pavelzazvorka-ctrl/AltiVario/doc/img/20200905_162352.jpg

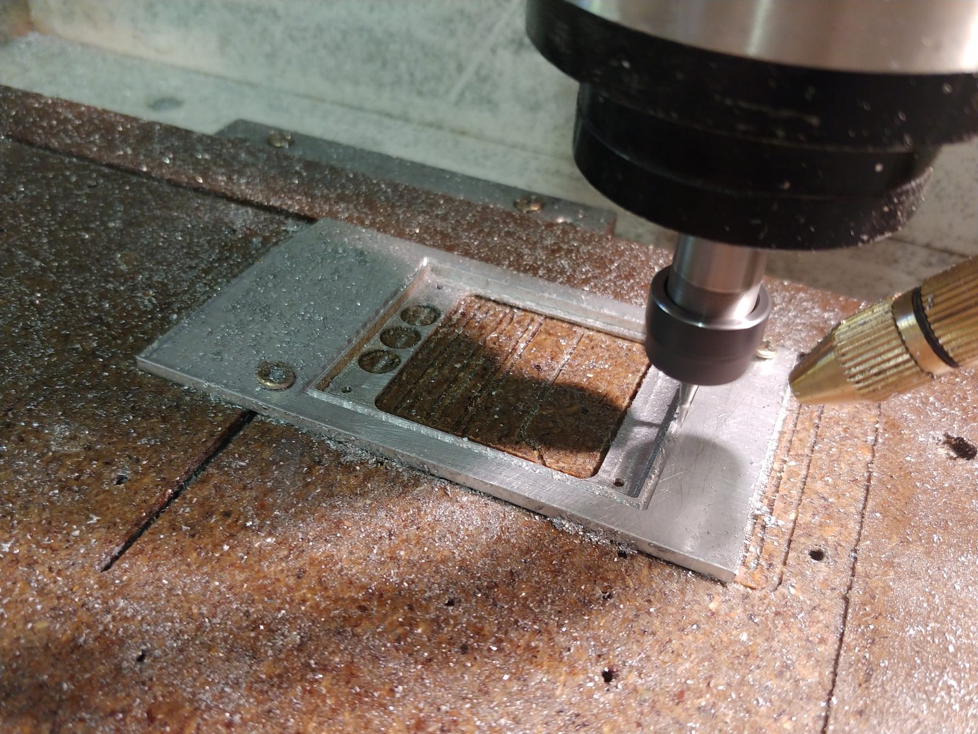
doc/img/20200905_162352.jpg
