pavelzazvorka-ctrl/AltiVario/doc/img/20200905_163800_HDR.jpg

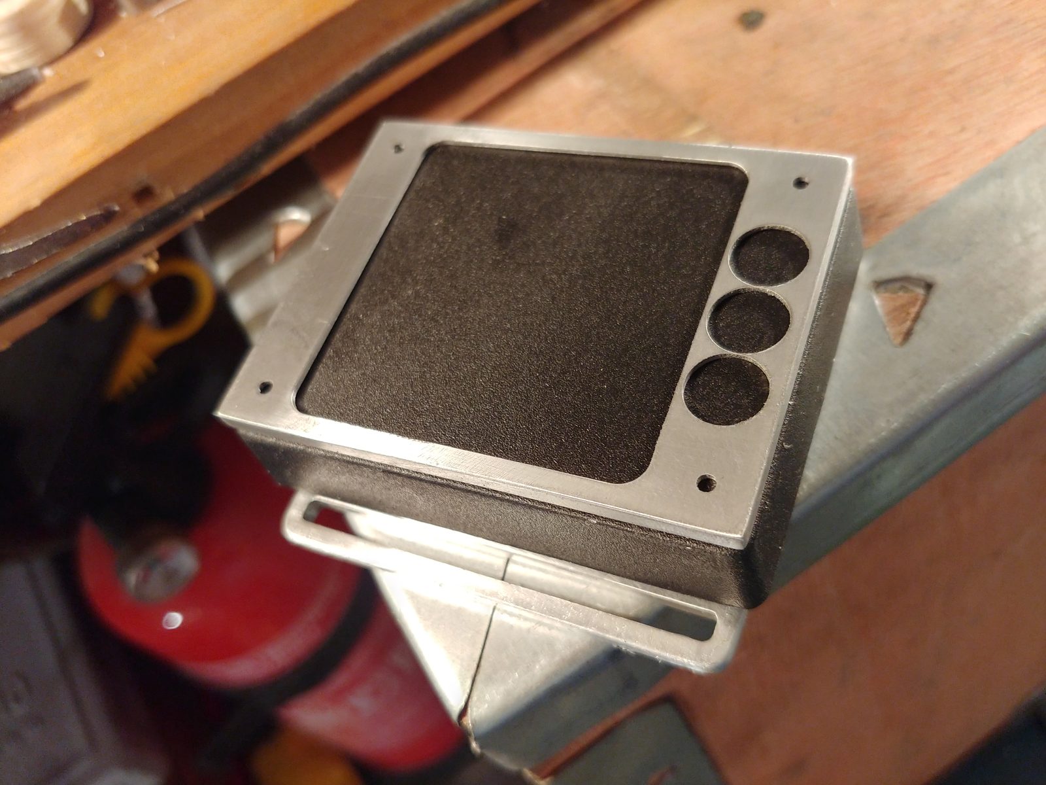
doc/img/20200905_163800_HDR.jpg
