pavelzazvorka-ctrl/AltiVario/doc/img/20200905_175942_HDR.jpg

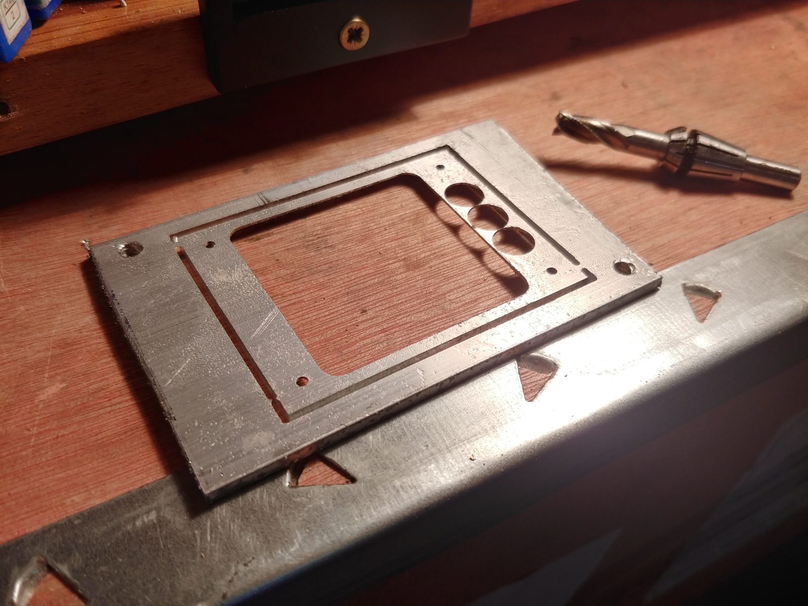
doc/img/20200905_175942_HDR.jpg
