pavelzazvorka-ctrl/AltiVario/doc/img/20200926_111940.jpg

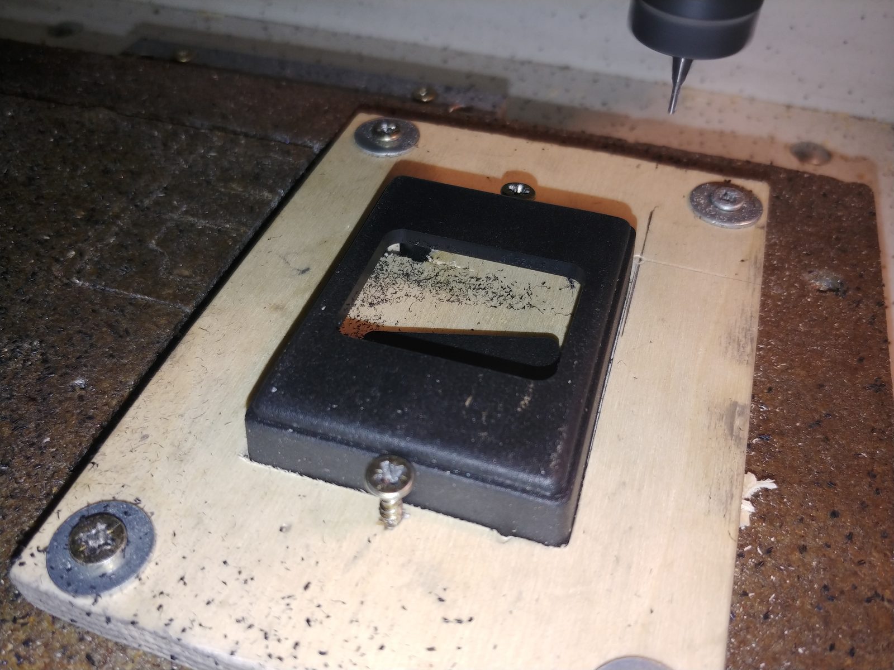
doc/img/20200926_111940.jpg
