pavelzazvorka-ctrl/AltiVario/doc/img/20200926_113900_HDR.jpg

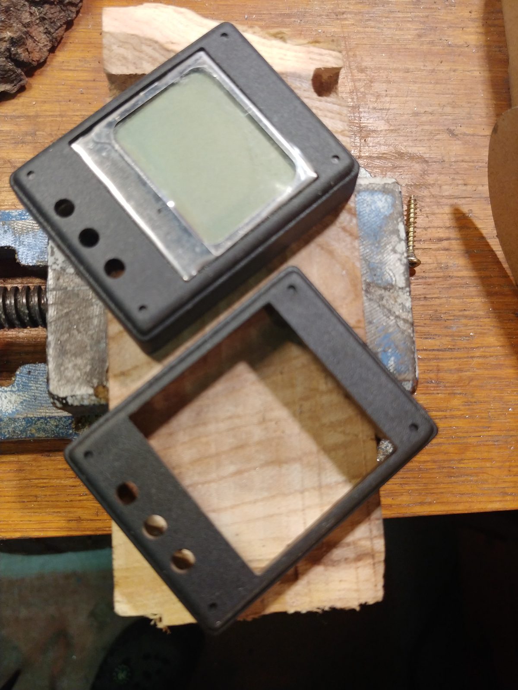
doc/img/20200926_113900_HDR.jpg
