pavelzazvorka-ctrl/AltiVario/doc/img/20200926_113952.jpg

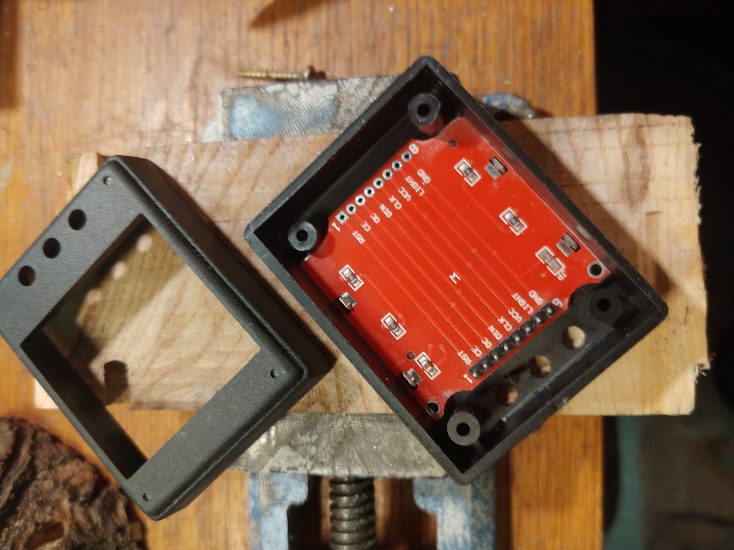
doc/img/20200926_113952.jpg
