pavelzazvorka-ctrl/AltiVario/doc/img/20200926_114129_HDR.jpg

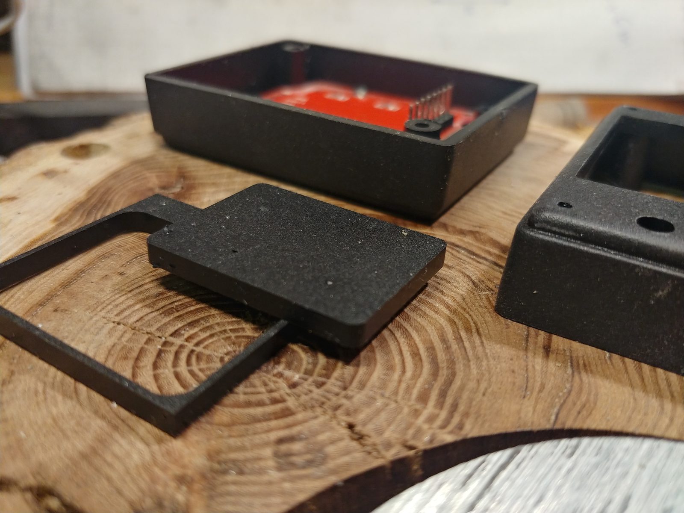
doc/img/20200926_114129_HDR.jpg
