pavelzazvorka-ctrl/AltiVario/doc/img/20200926_120201.jpg

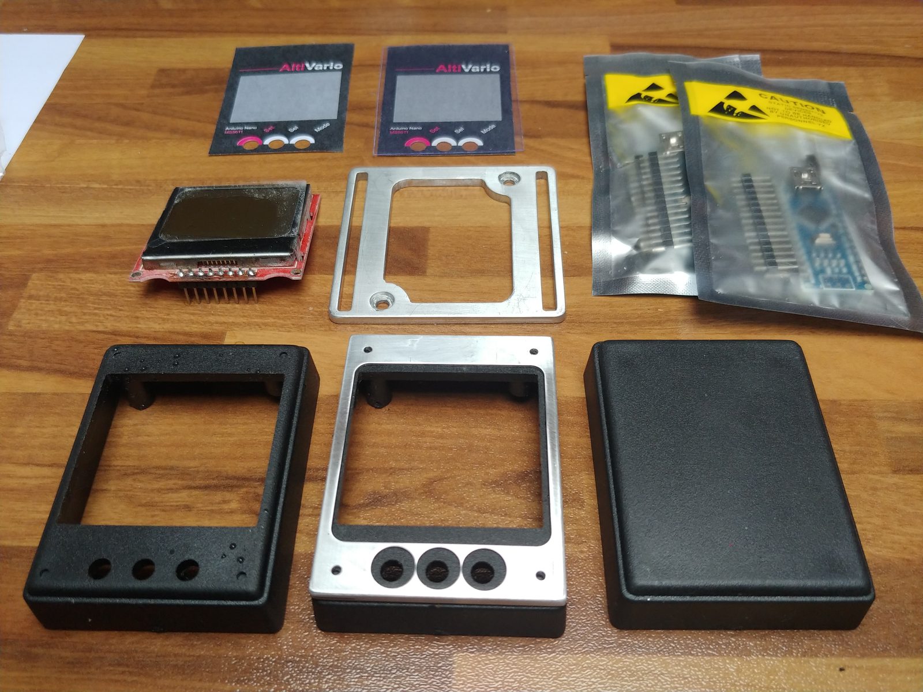
doc/img/20200926_120201.jpg
