pavelzazvorka-ctrl/AltiVario/doc/img/20200926_120225.jpg

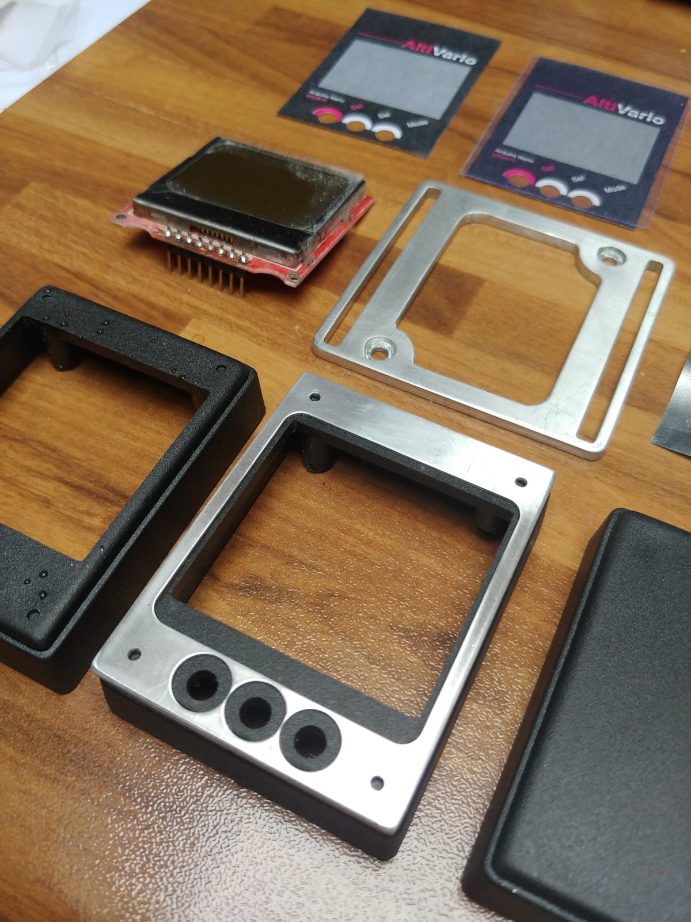
doc/img/20200926_120225.jpg
