pavelzazvorka-ctrl/AltiVario/doc/img/20200926_160403.jpg

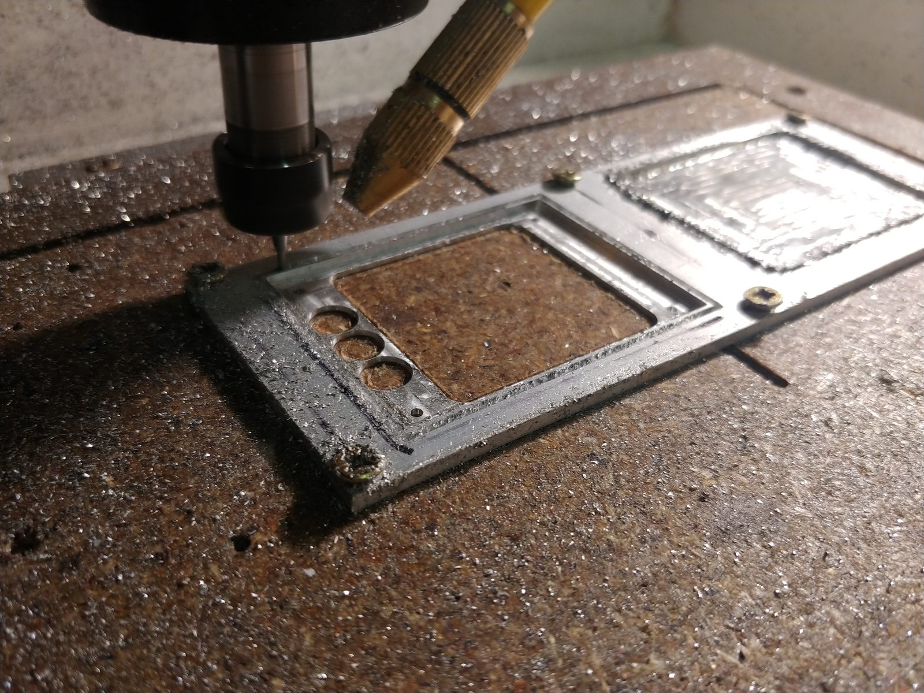
doc/img/20200926_160403.jpg
