pavelzazvorka-ctrl/AltiVario/doc/img/20200926_190031.jpg

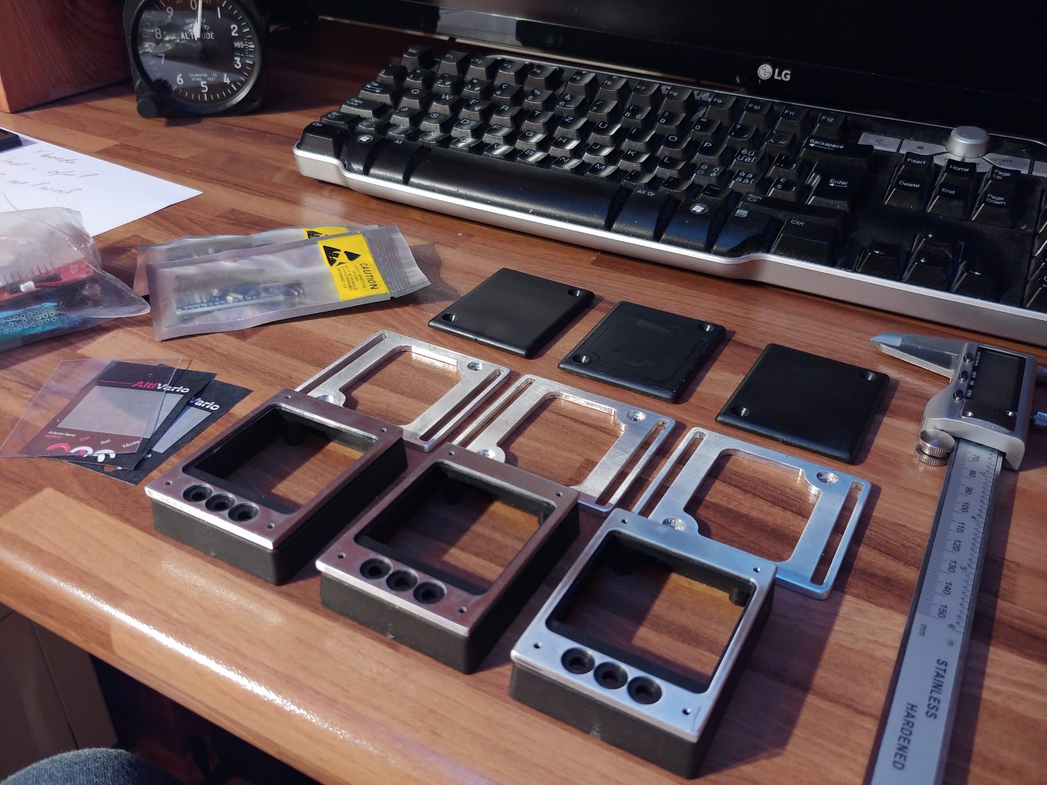
doc/img/20200926_190031.jpg
