pavelzazvorka-ctrl/AltiVario/doc/img/20200926_190852_HDR.jpg

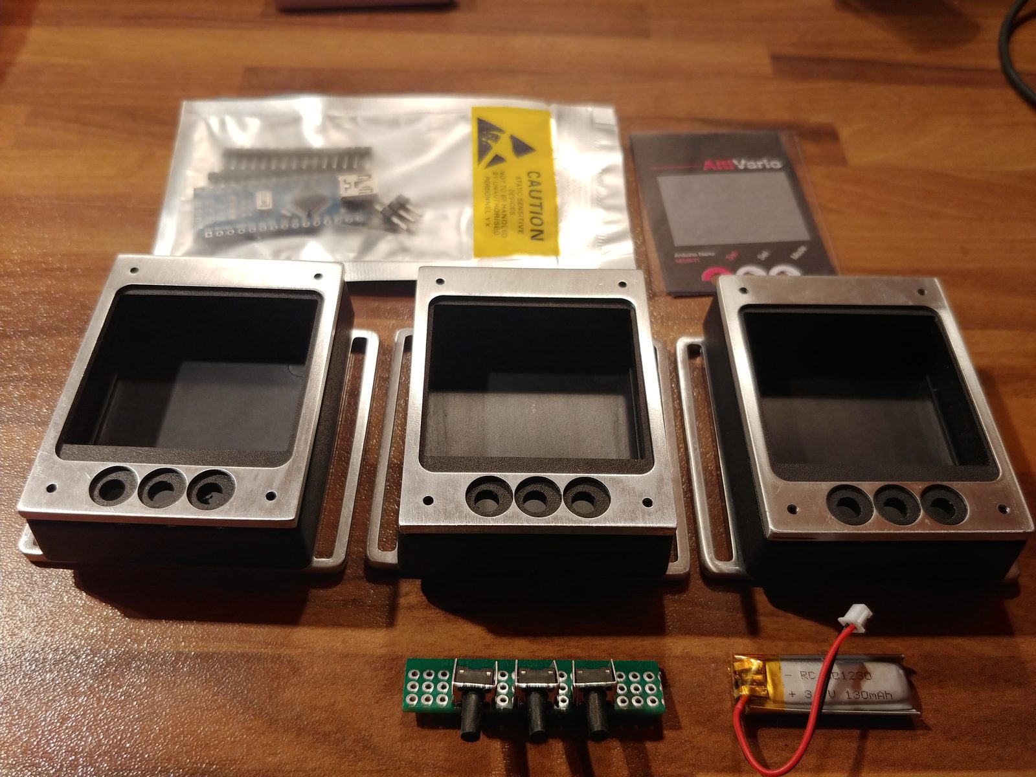
doc/img/20200926_190852_HDR.jpg
