pavelzazvorka-ctrl/AltiVario/doc/img/20200928_101642.jpg

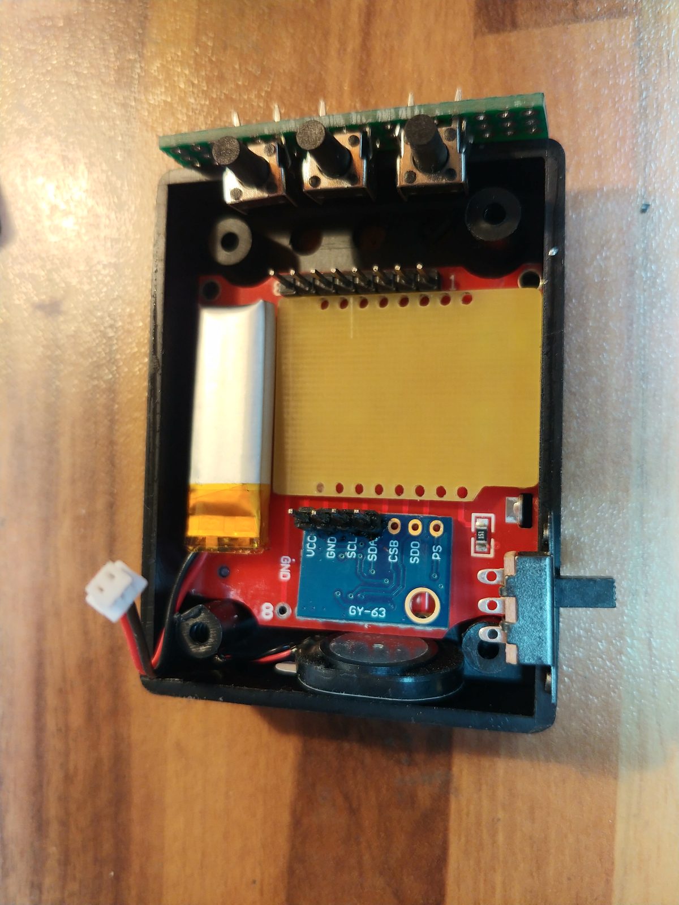
doc/img/20200928_101642.jpg
