pavelzazvorka-ctrl/AltiVario/doc/img/20200928_130921.jpg

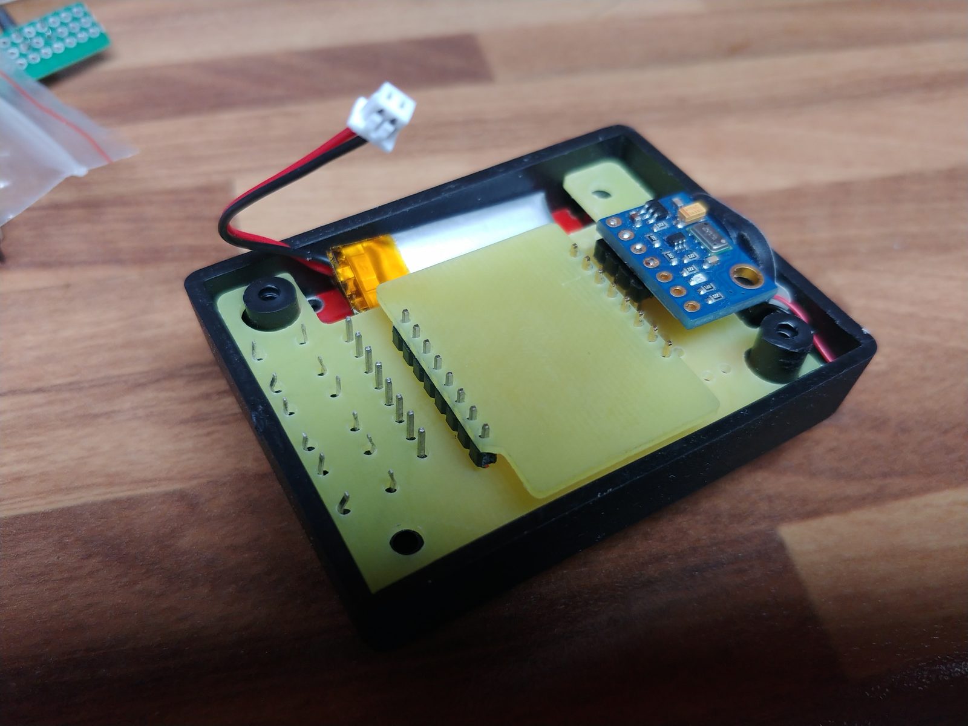
doc/img/20200928_130921.jpg
