pavelzazvorka-ctrl/AltiVario/doc/img/20200928_130946.jpg

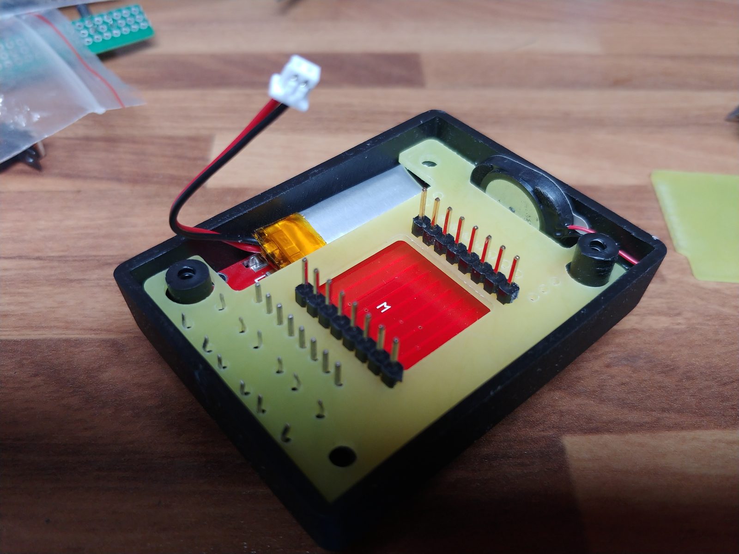
doc/img/20200928_130946.jpg
