pavelzazvorka-ctrl/AltiVario/doc/img/20200928_131029.jpg

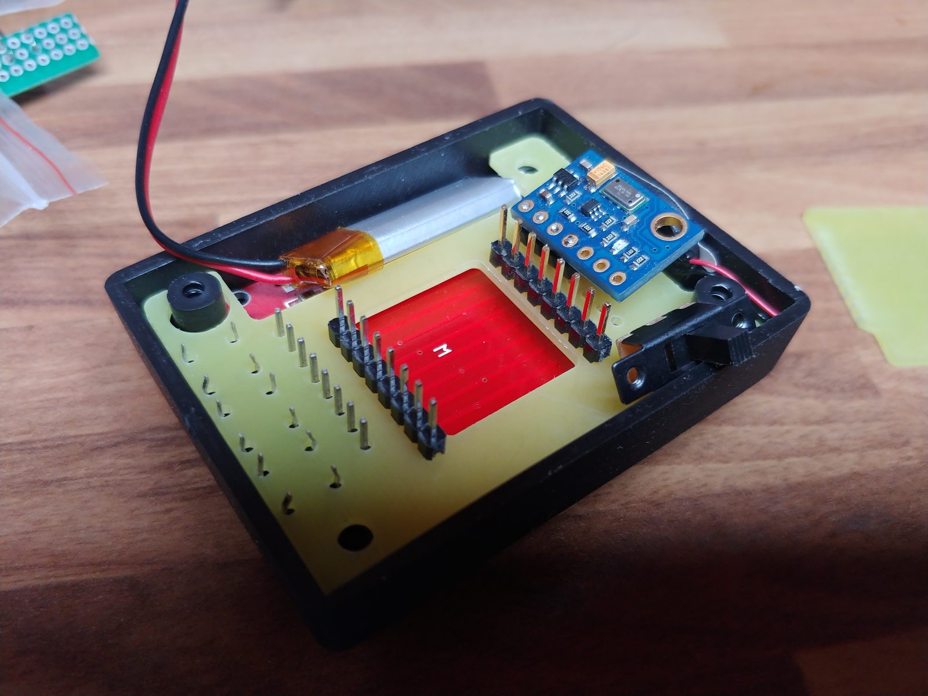
doc/img/20200928_131029.jpg
