pavelzazvorka-ctrl/AltiVario/doc/img/20200928_131043.jpg

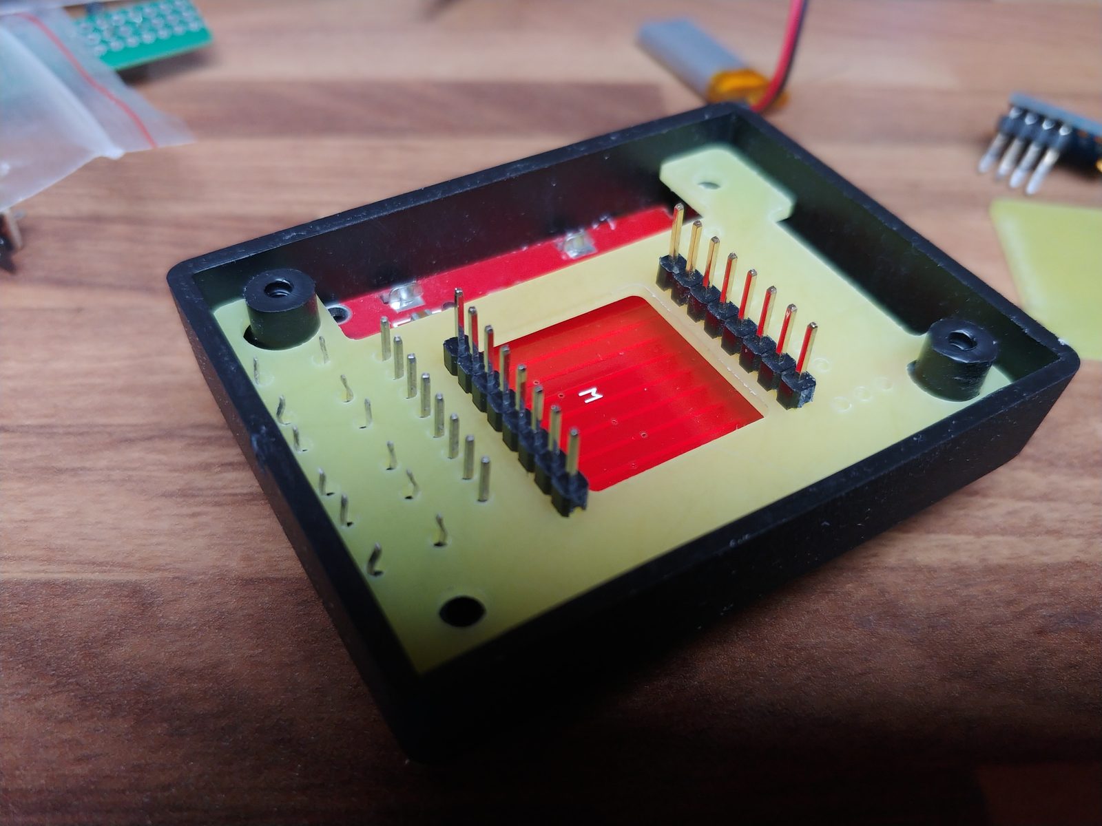
doc/img/20200928_131043.jpg
