pavelzazvorka-ctrl/AltiVario/doc/img/20200928_131057.jpg

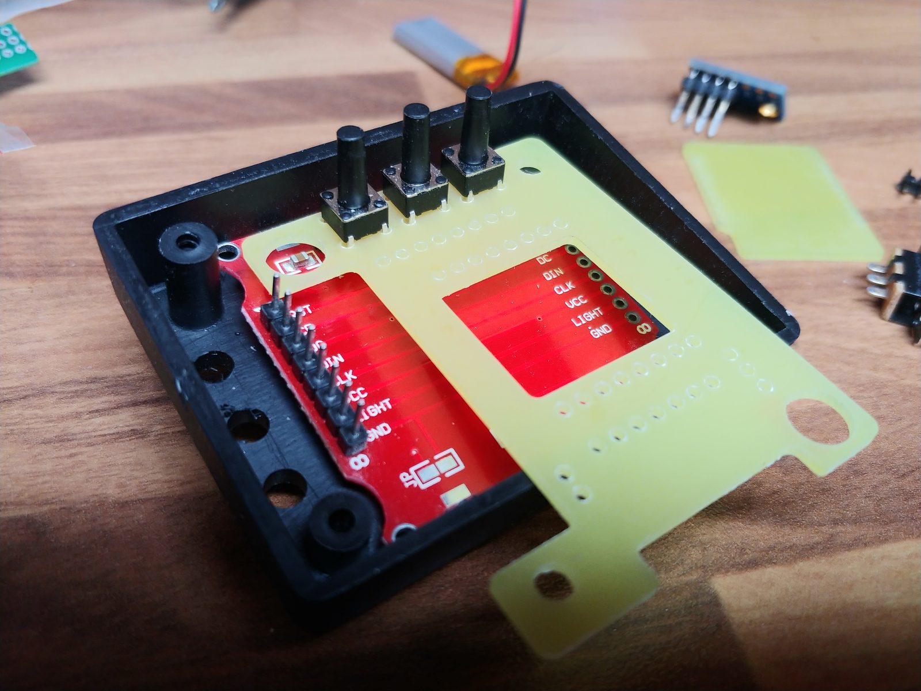
doc/img/20200928_131057.jpg
