pavelzazvorka-ctrl/AltiVario/doc/img/20200928_131132.jpg

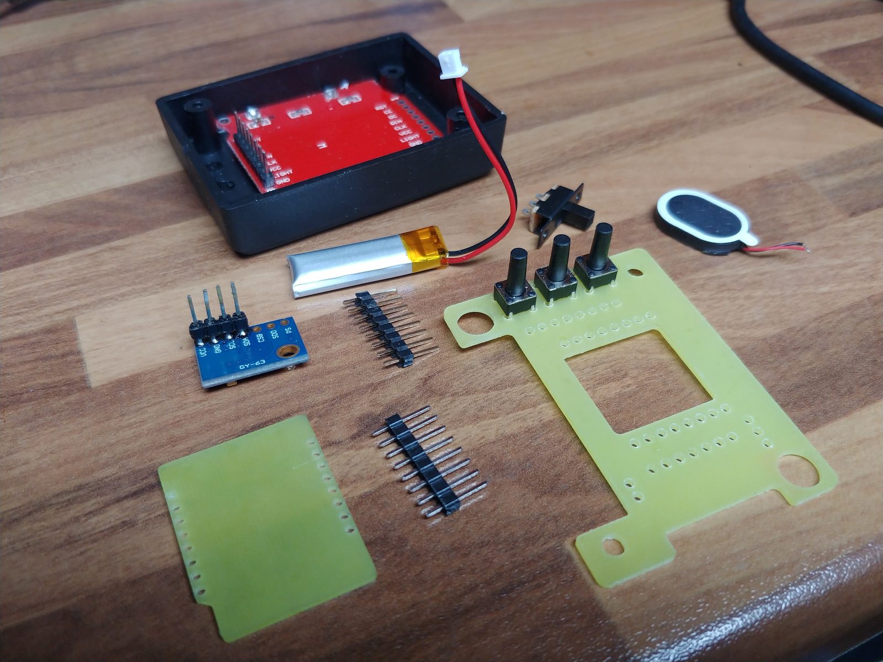
doc/img/20200928_131132.jpg
