pavelzazvorka-ctrl/AltiVario/doc/img/20201104_202439.jpg

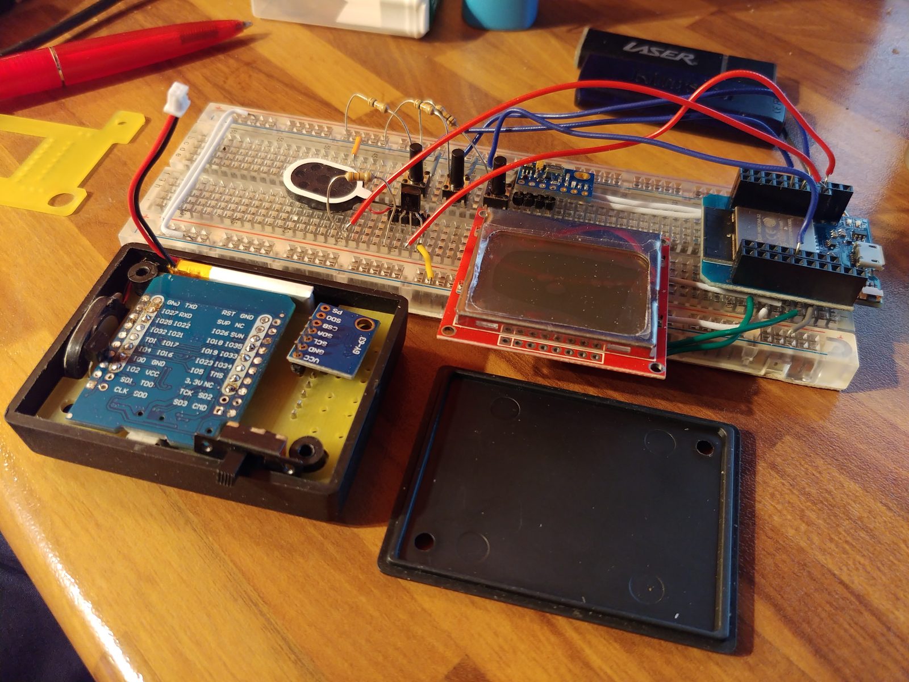
doc/img/20201104_202439.jpg
