pavelzazvorka-ctrl/AltiVario/doc/img/20201107_131443.jpg

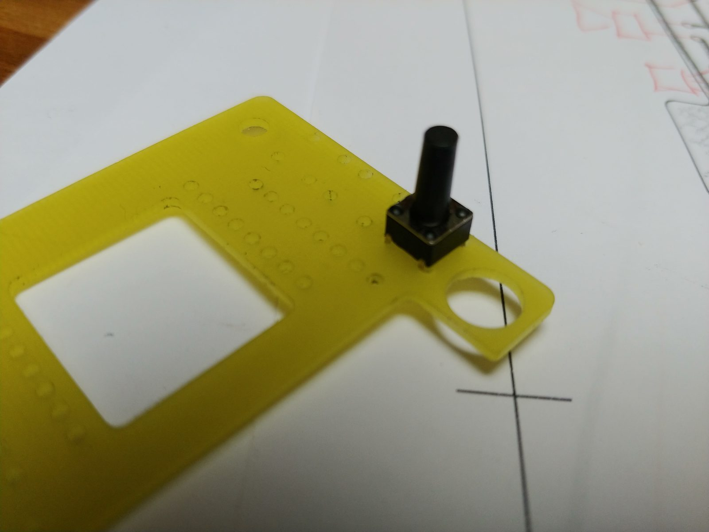
doc/img/20201107_131443.jpg
