pavelzazvorka-ctrl/AltiVario/doc/img/20201107_174315.jpg

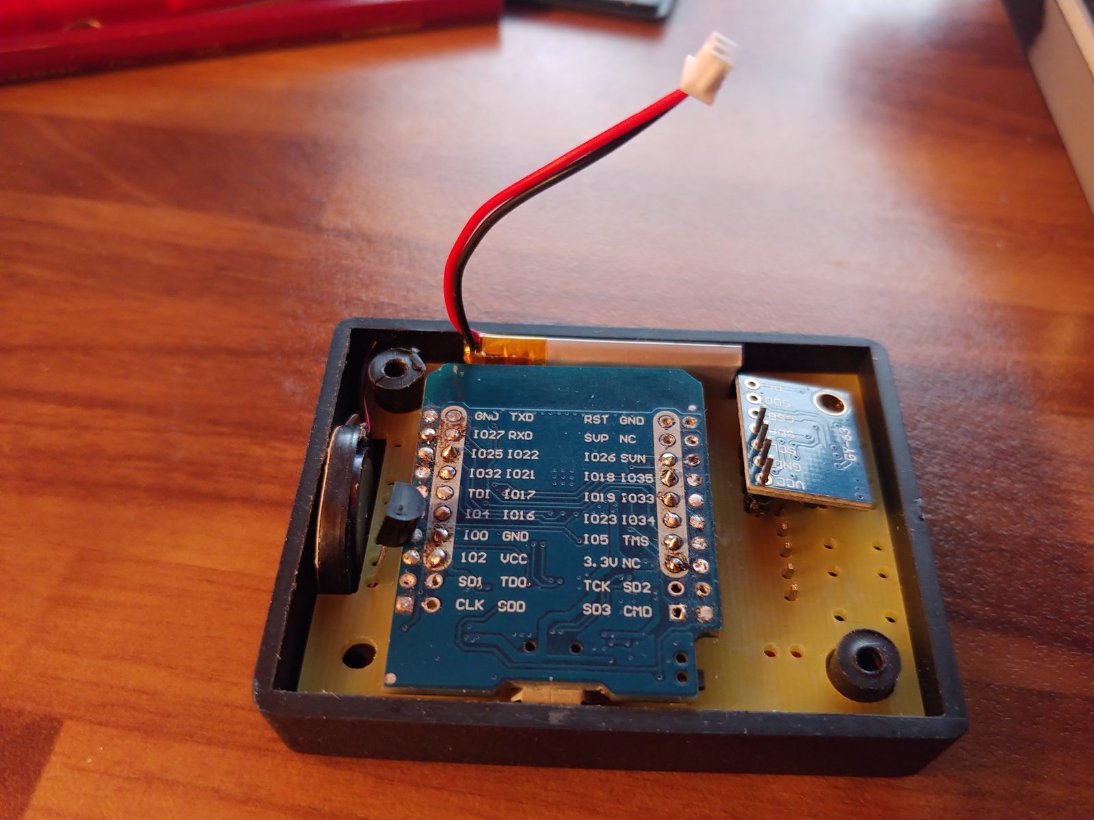
doc/img/20201107_174315.jpg
