pavelzazvorka-ctrl/AltiVario/doc/img/20201108_122216.jpg

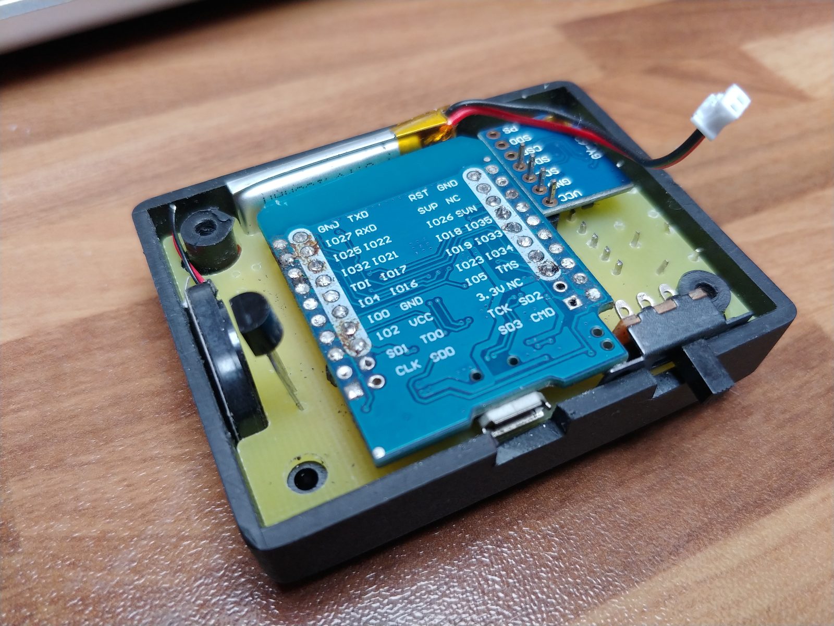
doc/img/20201108_122216.jpg
