pavelzazvorka-ctrl/AltiVario/doc/img/20201128_163405.jpg

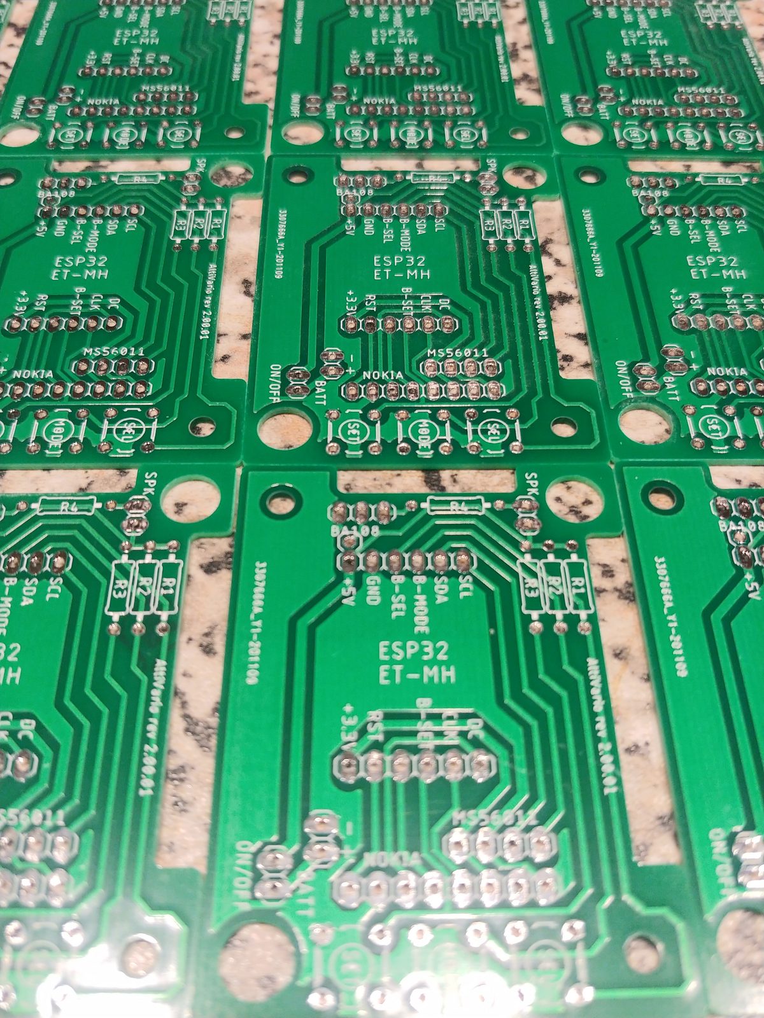
doc/img/20201128_163405.jpg
