pavelzazvorka-ctrl/AltiVario/doc/img/20201128_163448.jpg

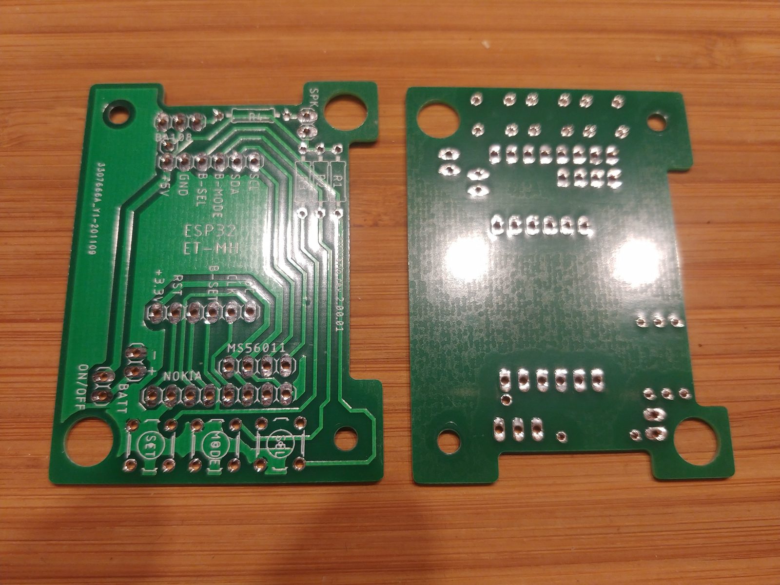
doc/img/20201128_163448.jpg
