pavelzazvorka-ctrl/AltiVario/doc/img/20201128_163759.jpg

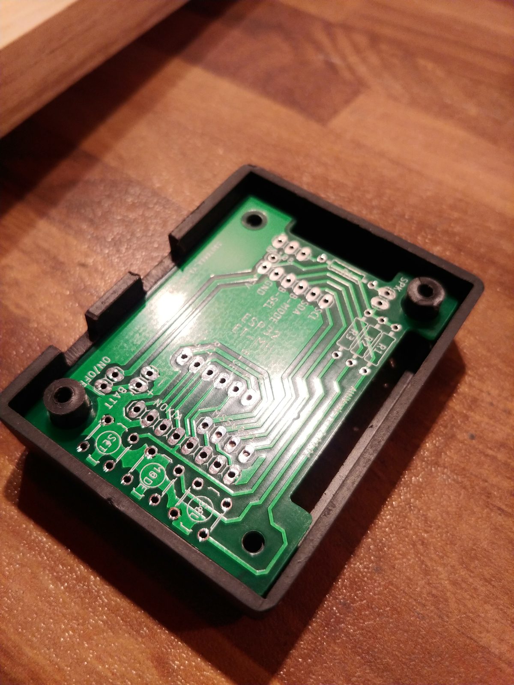
doc/img/20201128_163759.jpg
