pavelzazvorka-ctrl/AltiVario/doc/img/20201128_184807.jpg

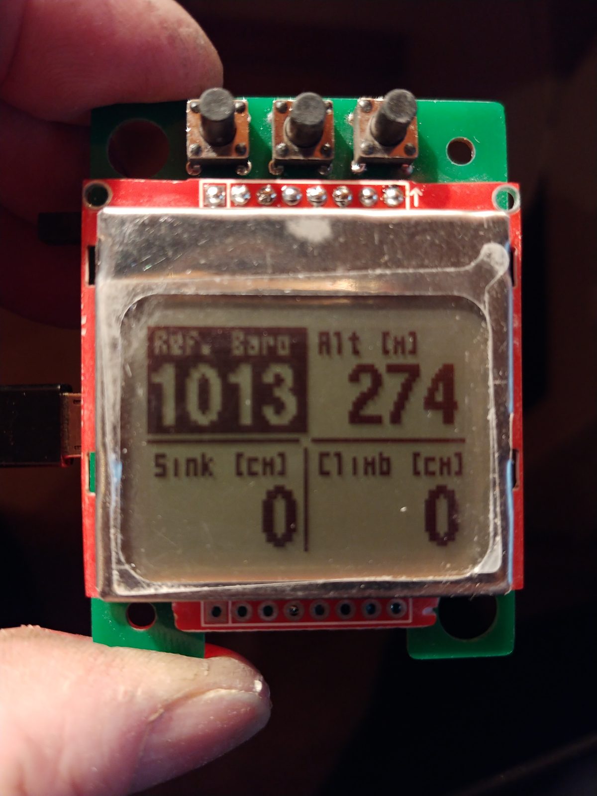
doc/img/20201128_184807.jpg
