pavelzazvorka-ctrl/AltiVario/doc/img/20201128_184845.jpg

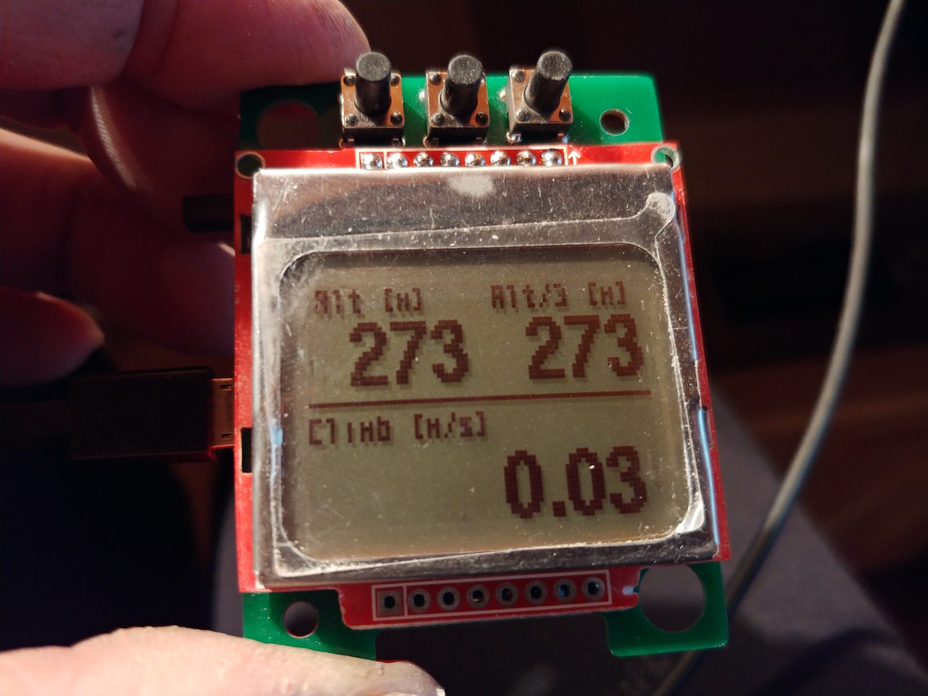
doc/img/20201128_184845.jpg
