pavelzazvorka-ctrl/AltiVario/doc/img/20201128_184942.jpg

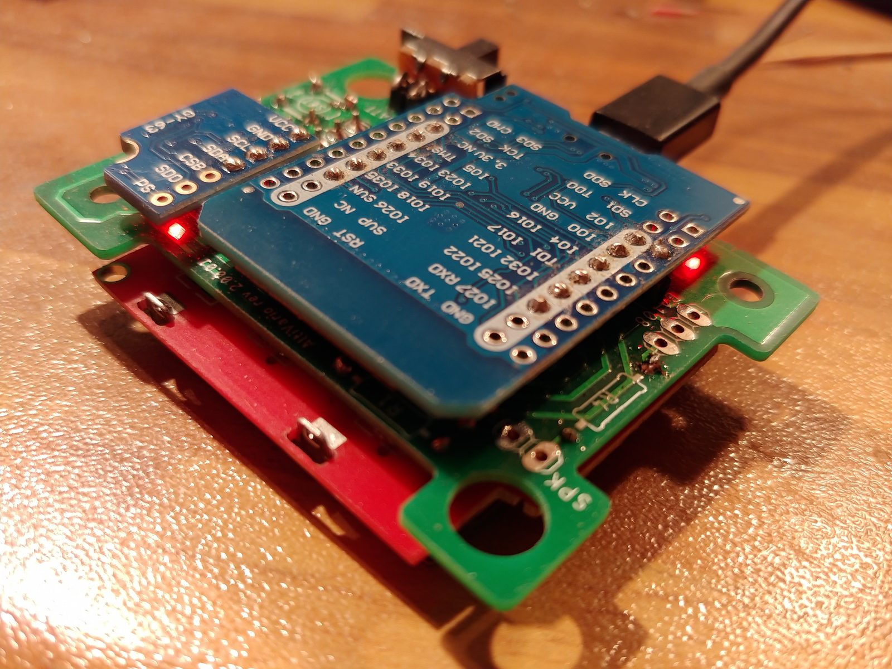
doc/img/20201128_184942.jpg
