pavelzazvorka-ctrl/AltiVario/doc/img/20201128_184955.jpg

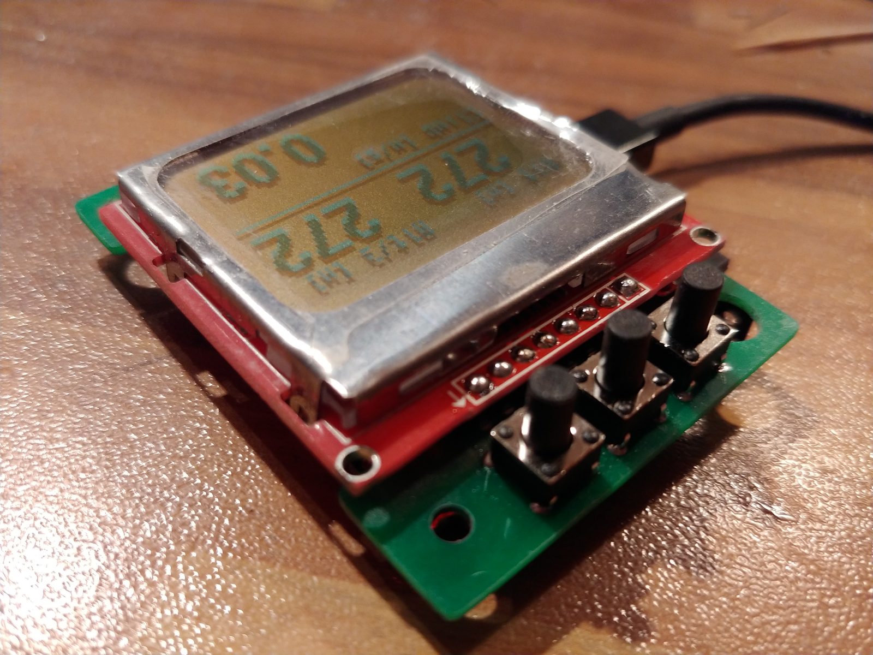
doc/img/20201128_184955.jpg
