pavelzazvorka-ctrl/AltiVario/doc/img/20201128_190515.jpg

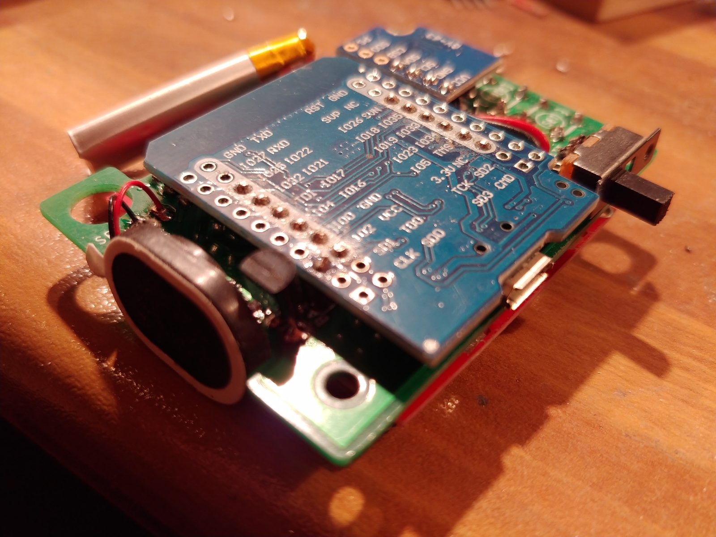
doc/img/20201128_190515.jpg
