pavelzazvorka-ctrl/AltiVario/doc/img/20201128_191132.jpg

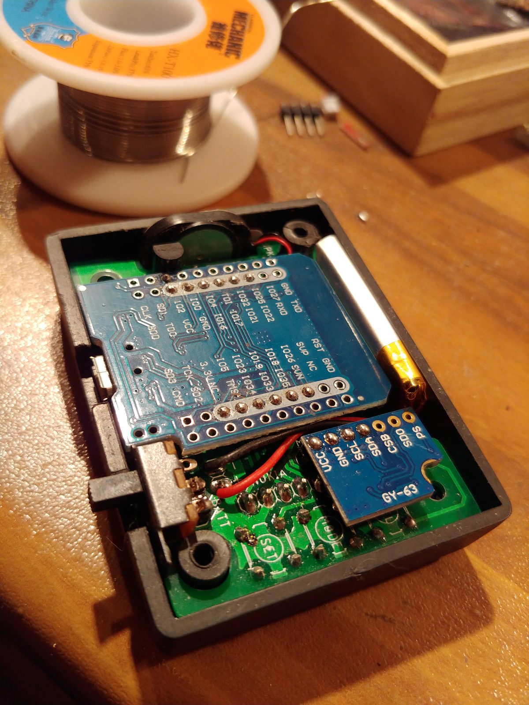
doc/img/20201128_191132.jpg
