pavelzazvorka-ctrl/AltiVario/doc/img/20201128_191707_HDR.jpg

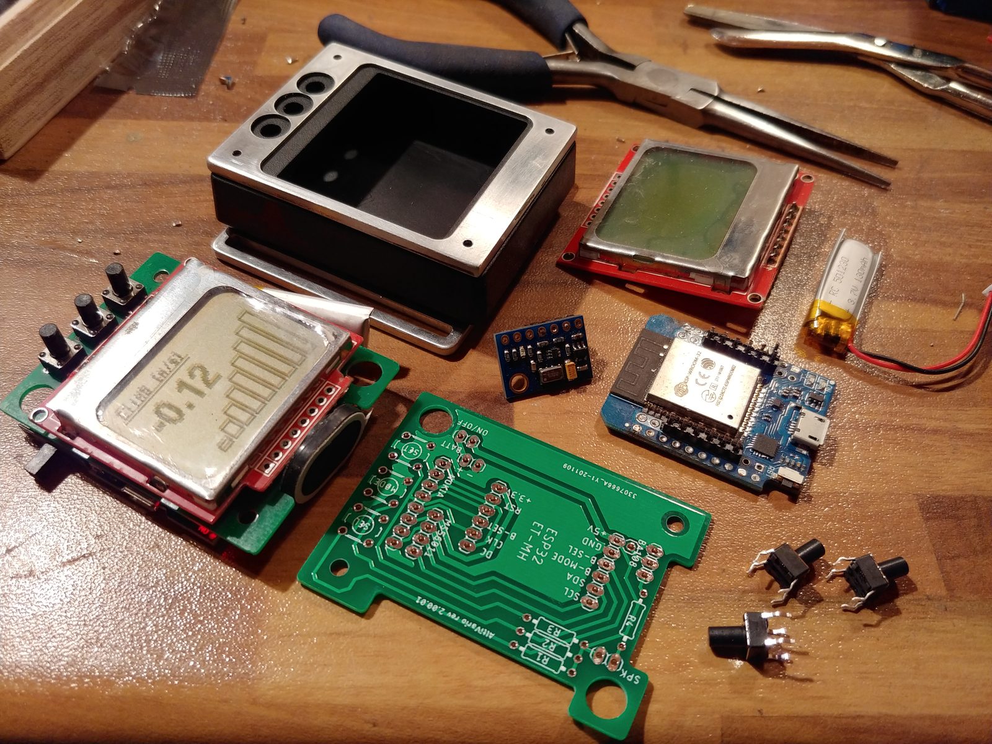
doc/img/20201128_191707_HDR.jpg
