pavelzazvorka-ctrl/AltiVario/doc/img/20201222_194139.jpg

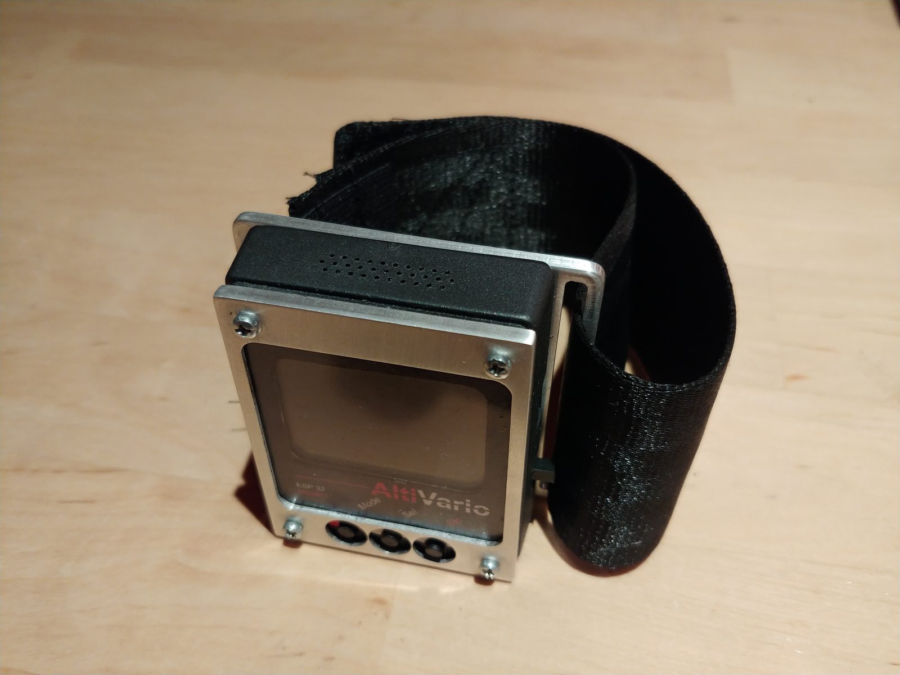
doc/img/20201222_194139.jpg
