pavelzazvorka-ctrl/AltiVario/doc/img/20201230_100213.jpg

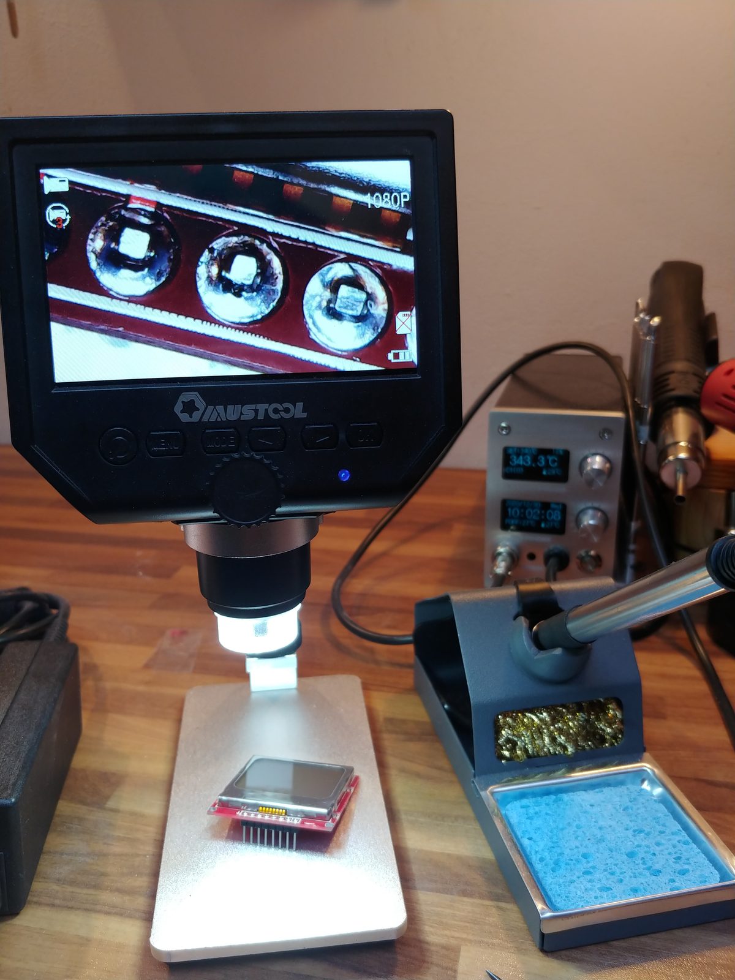
doc/img/20201230_100213.jpg
