pavelzazvorka-ctrl/AltiVario/doc/img/20201230_100407.jpg

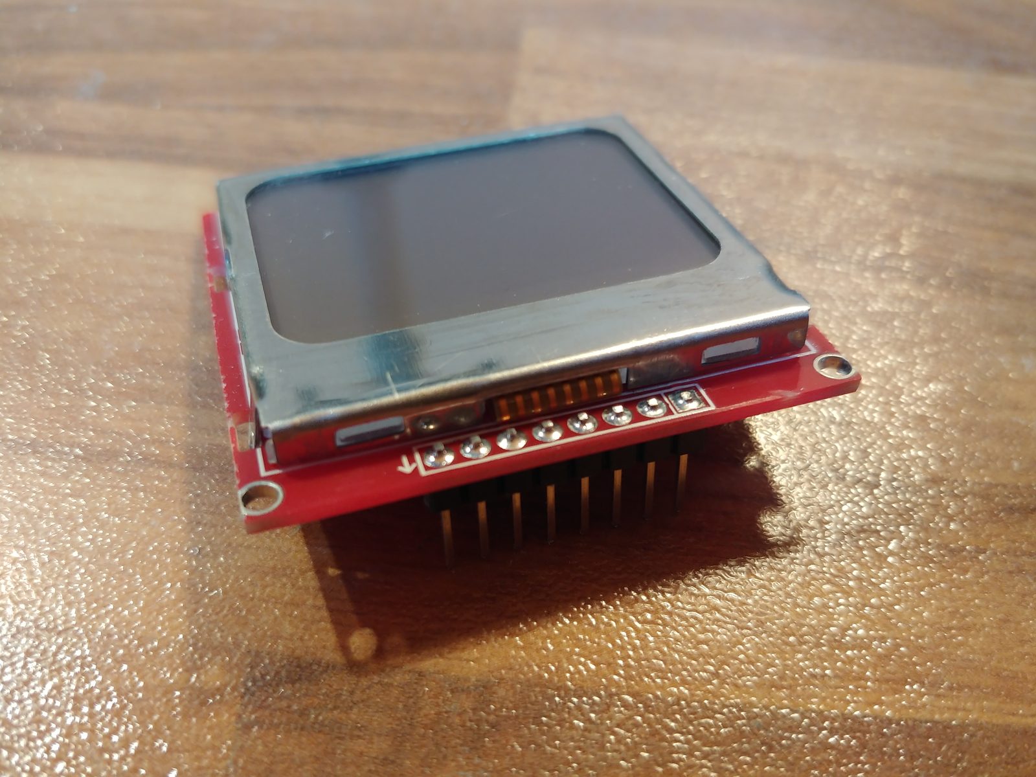
doc/img/20201230_100407.jpg
