pavelzazvorka-ctrl/AltiVario/doc/img/20210102_154831.jpg

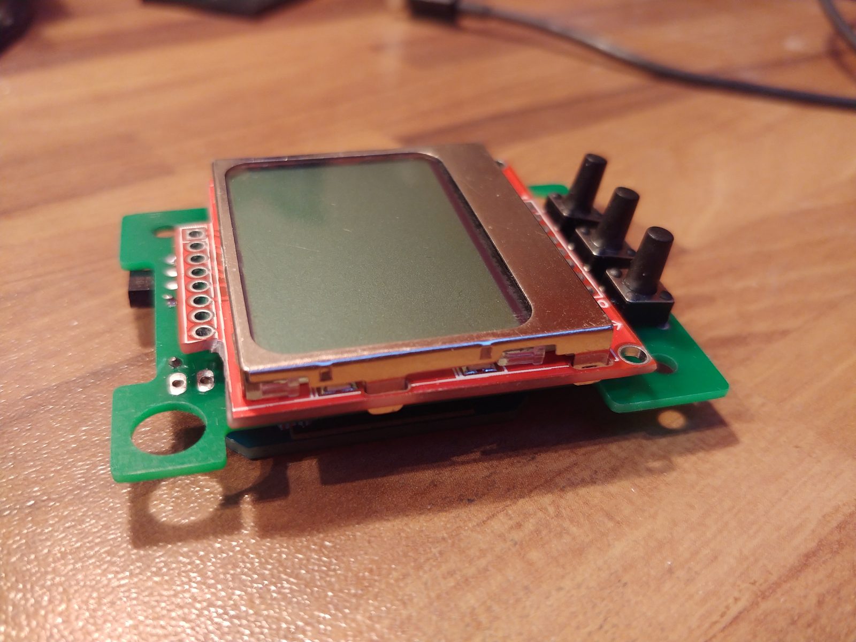
doc/img/20210102_154831.jpg
