pavelzazvorka-ctrl/AltiVario/doc/img/20210102_154841.jpg

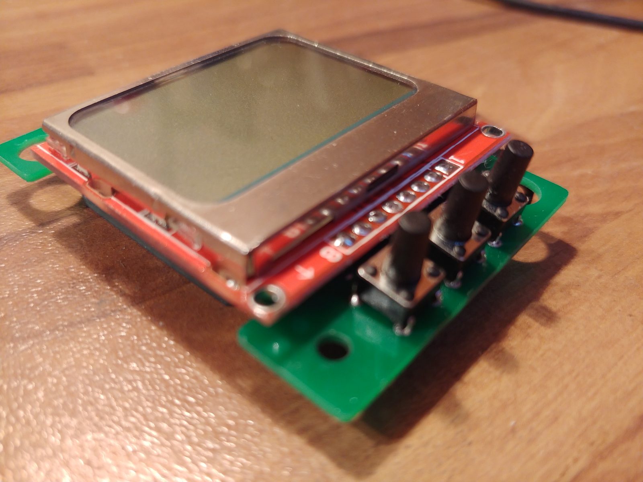
doc/img/20210102_154841.jpg
