pavelzazvorka-ctrl/AltiVario/doc/img/20210102_154853.jpg

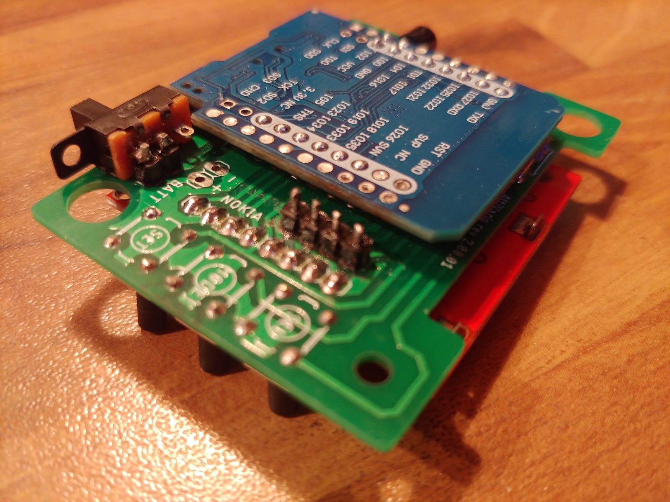
doc/img/20210102_154853.jpg
