pavelzazvorka-ctrl/AltiVario/doc/img/20210102_154902.jpg

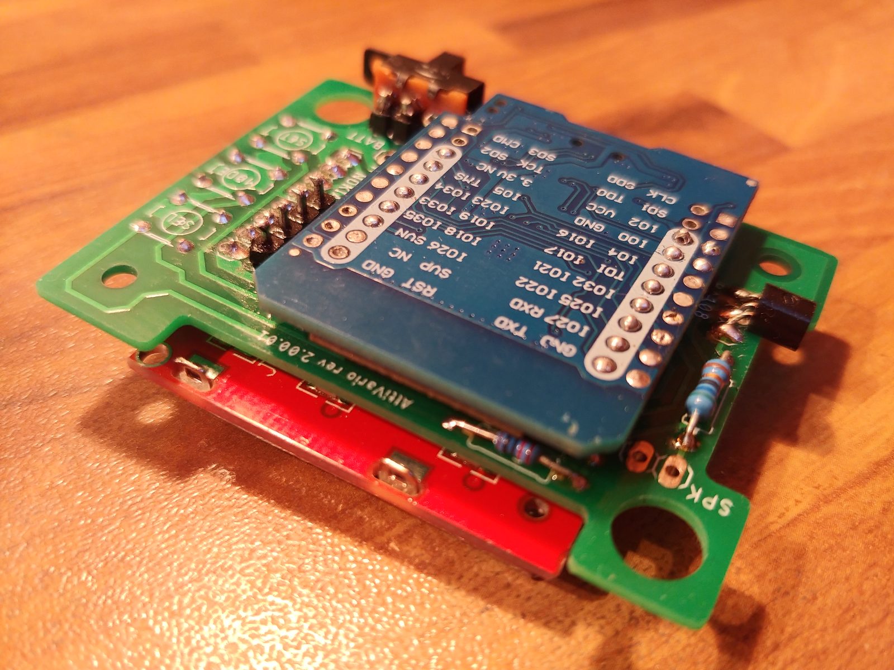
doc/img/20210102_154902.jpg
