pavelzazvorka-ctrl/AltiVario/doc/img/20210103_171847.jpg

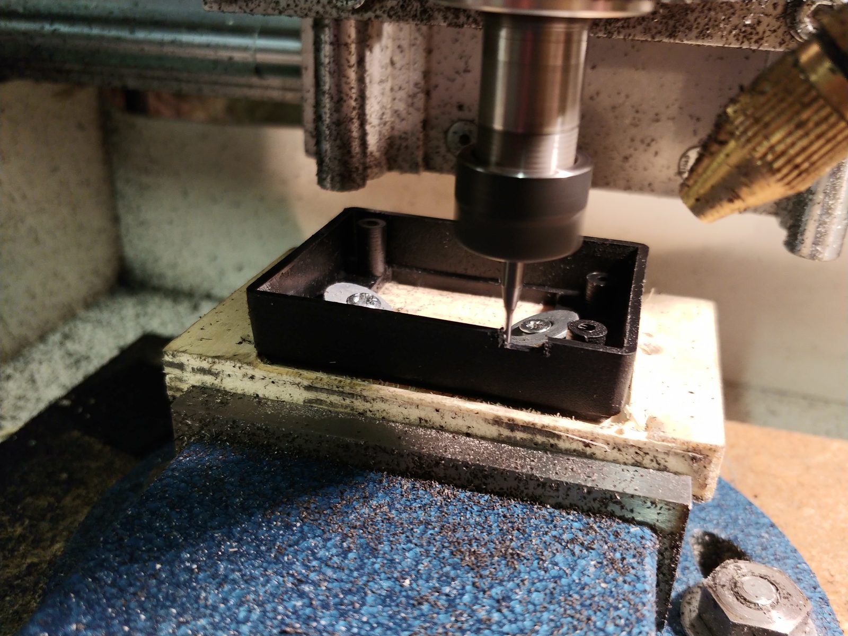
doc/img/20210103_171847.jpg
