pavelzazvorka-ctrl/AltiVario/doc/img/20210127_181344_HDR.jpg

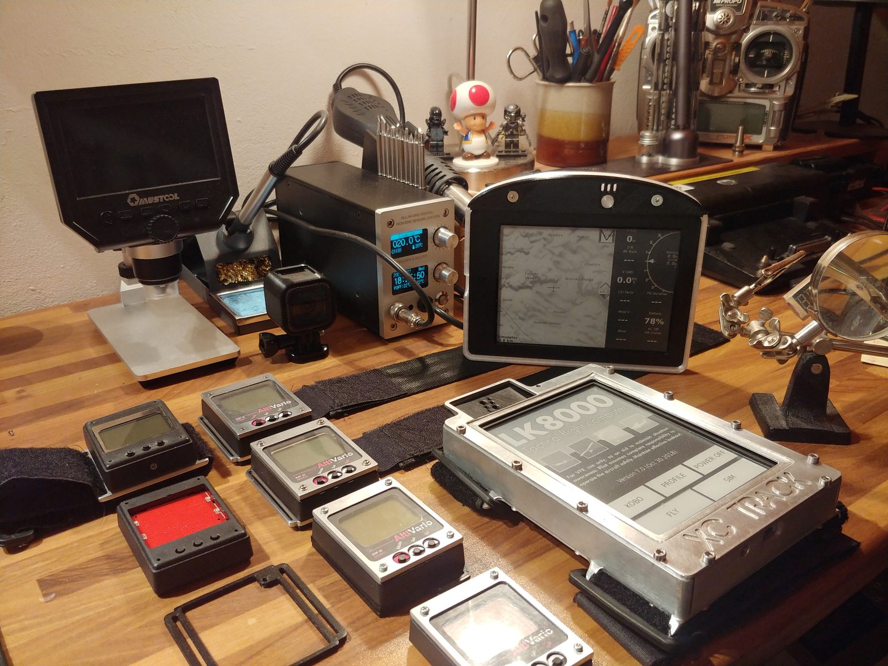
doc/img/20210127_181344_HDR.jpg
