pavelzazvorka-ctrl/AltiVario/doc/img/20210130_150703.jpg

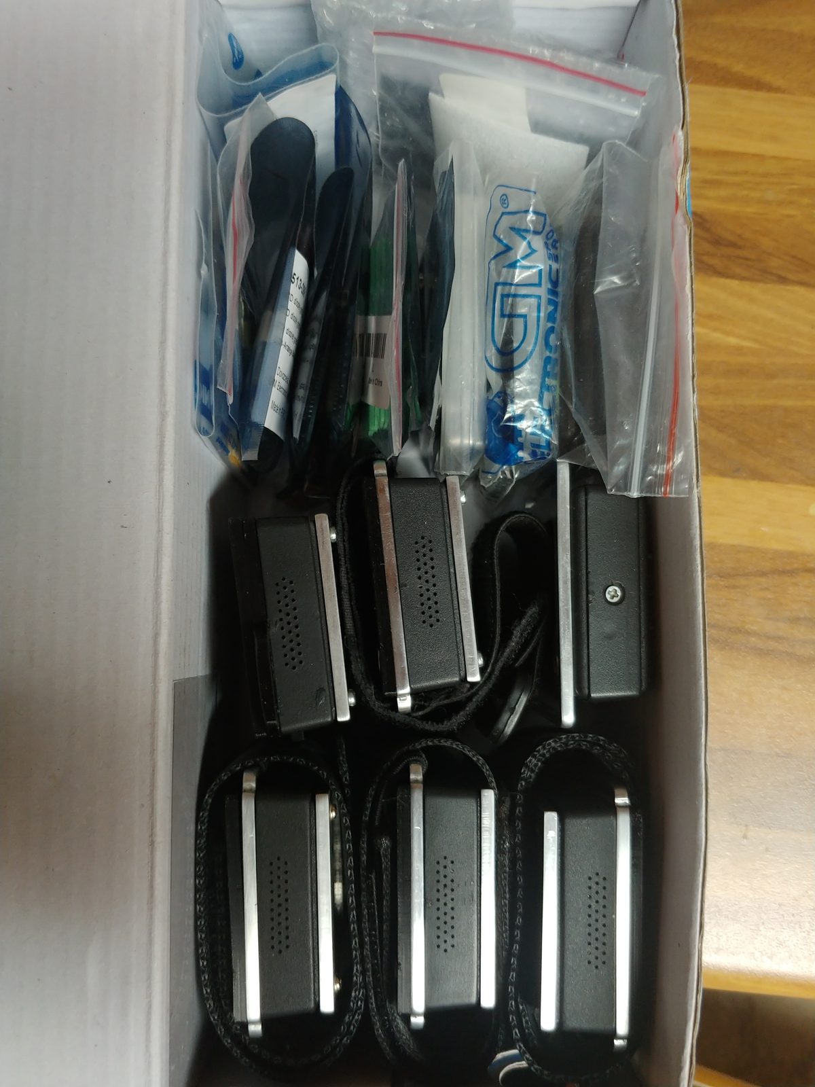
doc/img/20210130_150703.jpg
