pavelzazvorka-ctrl/AltiVario/svg/vario v2 shift.jpg

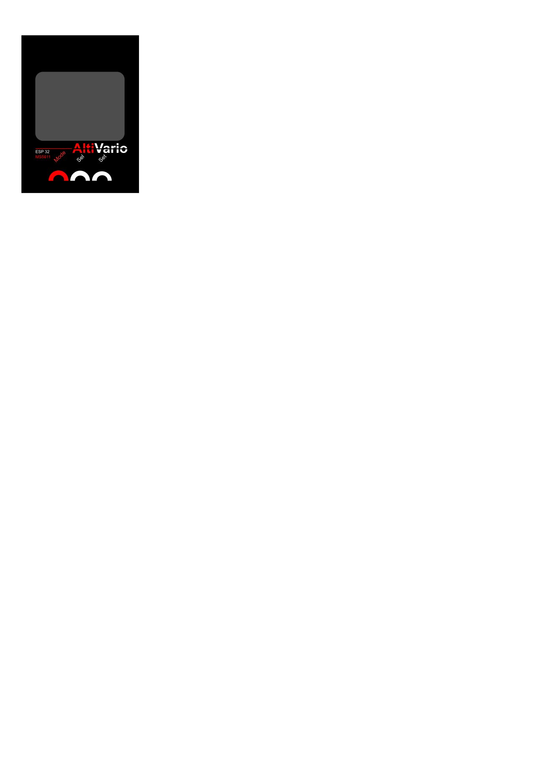
svg/vario v2 shift.jpg
