pavelzazvorka-ctrl/AltiVario/svg/vario v3.jpg

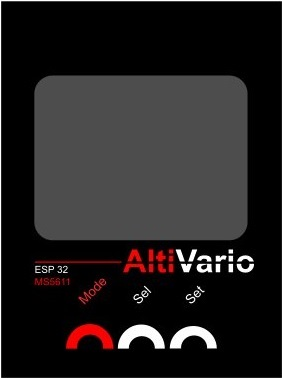
svg/vario v3.jpg
