pavelzazvorka-ctrl/AltiVario/src/Altvario - Multicore/Altvario/Atmosphere.cpp

/* 
  KDR Vario. Digital variometer based on Arduino.
  Copyright (C) 2011 Andrey Lebedev

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
  You should have received a copy of the GNU General Public License
  along with this program.  If not, see <http://www.gnu.org/licenses/>.
*/
#include <math.h>
#include "atmosphere.h"

const float stdpressure = 1013.25;

Atmosphere::Atmosphere() {
	_zeropressure = stdpressure;
}

void Atmosphere::setZeroPressure(float _altitude, float _pressure, float _temperature) {
  float zp = _altitude * 0.0065 / (_temperature + 273.15);
  zp = zp + 1;
  zp = pow ( zp, 5.257);
  zp = zp * _pressure;
  _zeropressure = zp;
}

float Atmosphere::getAltitude(float pressure, float temperature) {
  return ((pow((_zeropressure / pressure), 1/5.257) - 1.0) * (temperature + 273.15)) / 0.0065;
}

float Atmosphere::getZeroPressure() {
	return _zeropressure;
}

void Atmosphere::setZeroPressure(float zeropressure) {
	_zeropressure = zeropressure;
}
